ishaanashok/LUNA-TurbiditySensor/Project_LUNA_Images/IMG_0178.jpg

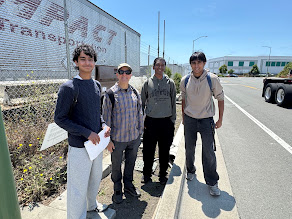
Project_LUNA_Images/IMG_0178.jpg
