ishaanashok/LUNA-TurbiditySensor/Project_LUNA_Images/IMG_7861.JPG

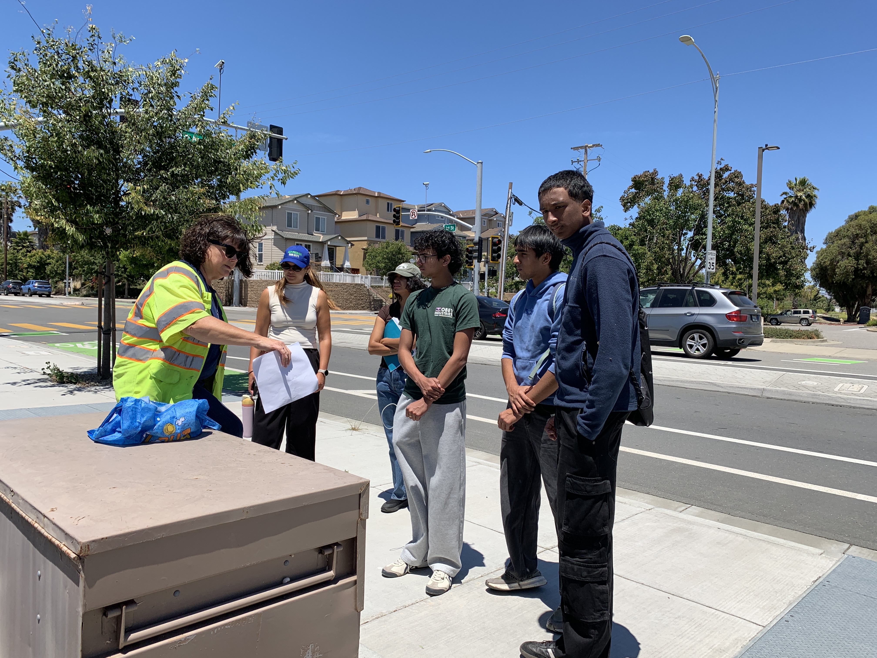
Project_LUNA_Images/IMG_7861.JPG
