ishaanashok/LUNA-TurbiditySensor/Inlet Sensor/v2/InletWiper.stl

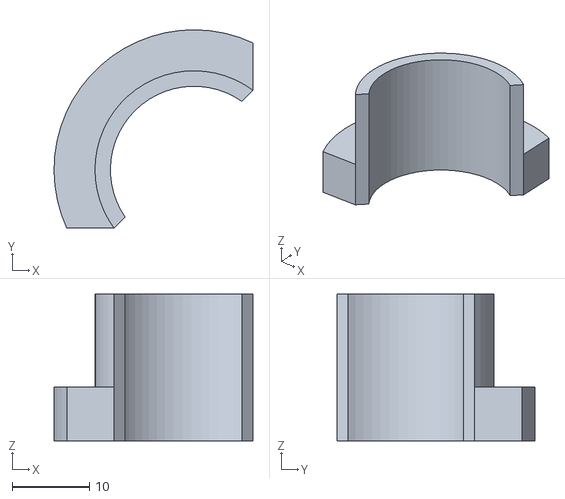
[picture p21: CAD file, 2026-08-10, an earlier design]
Inlet Sensor/v2/InletWiper.stl
25.7 x 25.7 x 19.0
