ishaanashok/LUNA-TurbiditySensor/Inlet Sensor/v2/InletSensor.stl

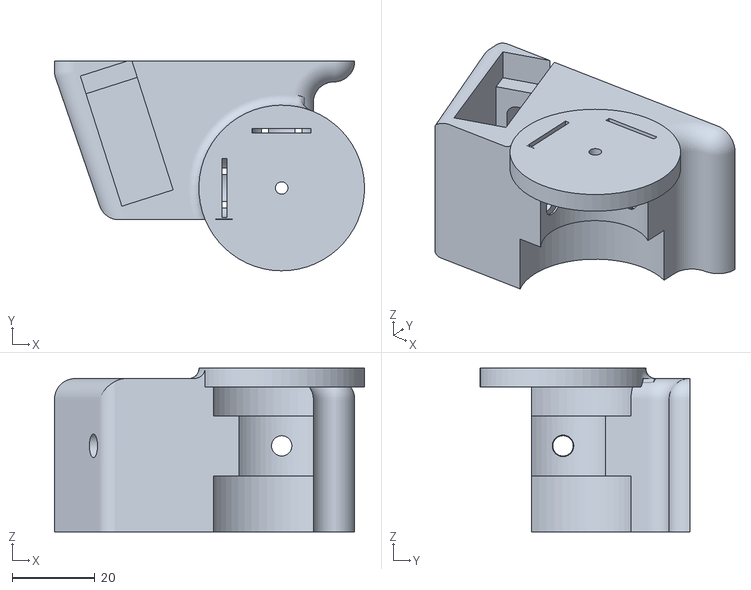
[picture p22: CAD file, 2026-08-10, an earlier design]
Inlet Sensor/v2/InletSensor.stl
74.9 x 50.6 x 39.5
