ishaanashok/LUNA-TurbiditySensor/Effluent Sensor/EffluentSensor - v1.stl

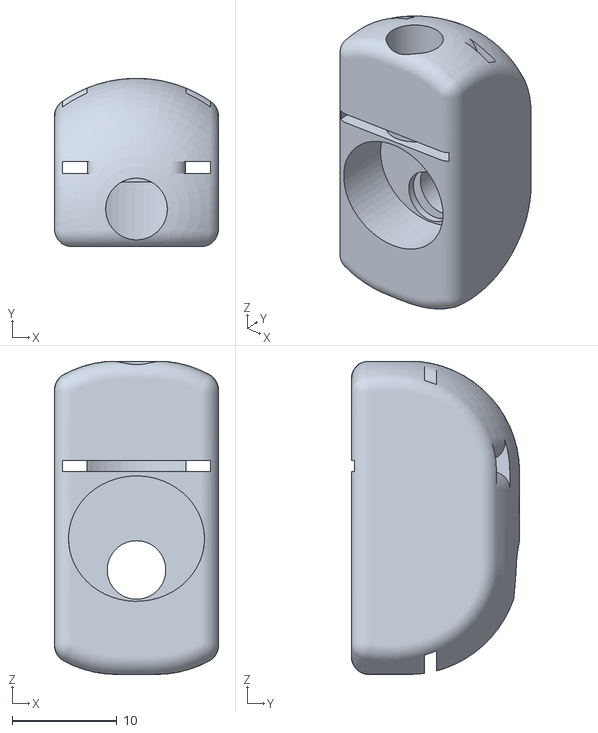
[picture p23: CAD file, 2026-08-10, an earlier design]
Effluent Sensor/EffluentSensor - v1.stl
15.7 x 16.1 x 29.9
